mnjoo-real/sc4/out/fig1_modes.png

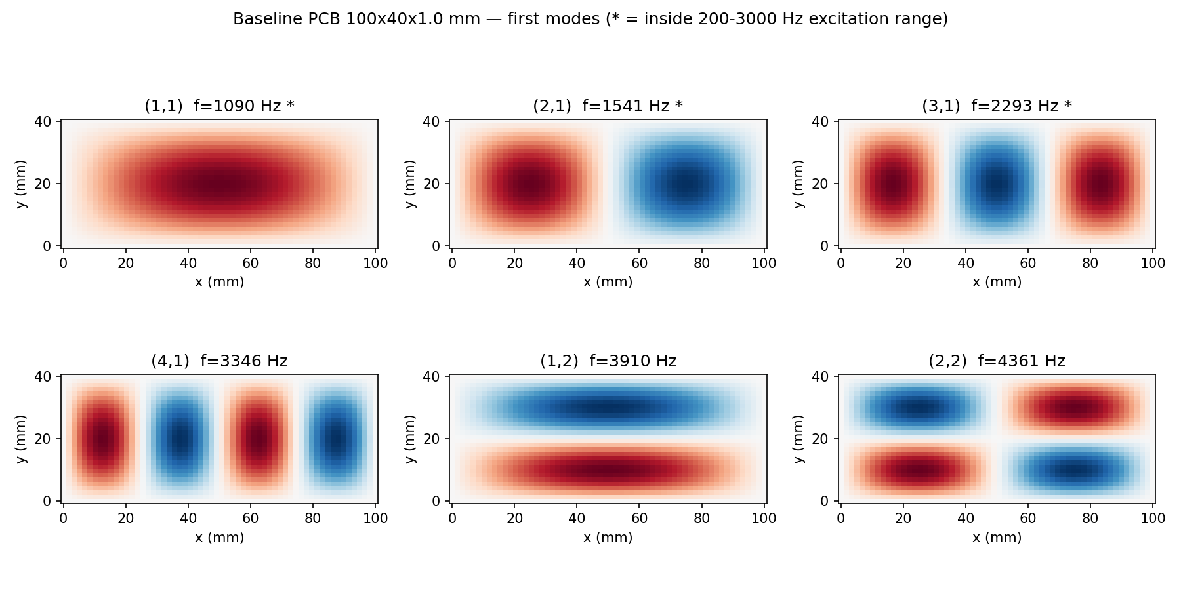
out/fig1_modes.png
