mnjoo-real/sc4/out/fig2_geometry_sweep.png

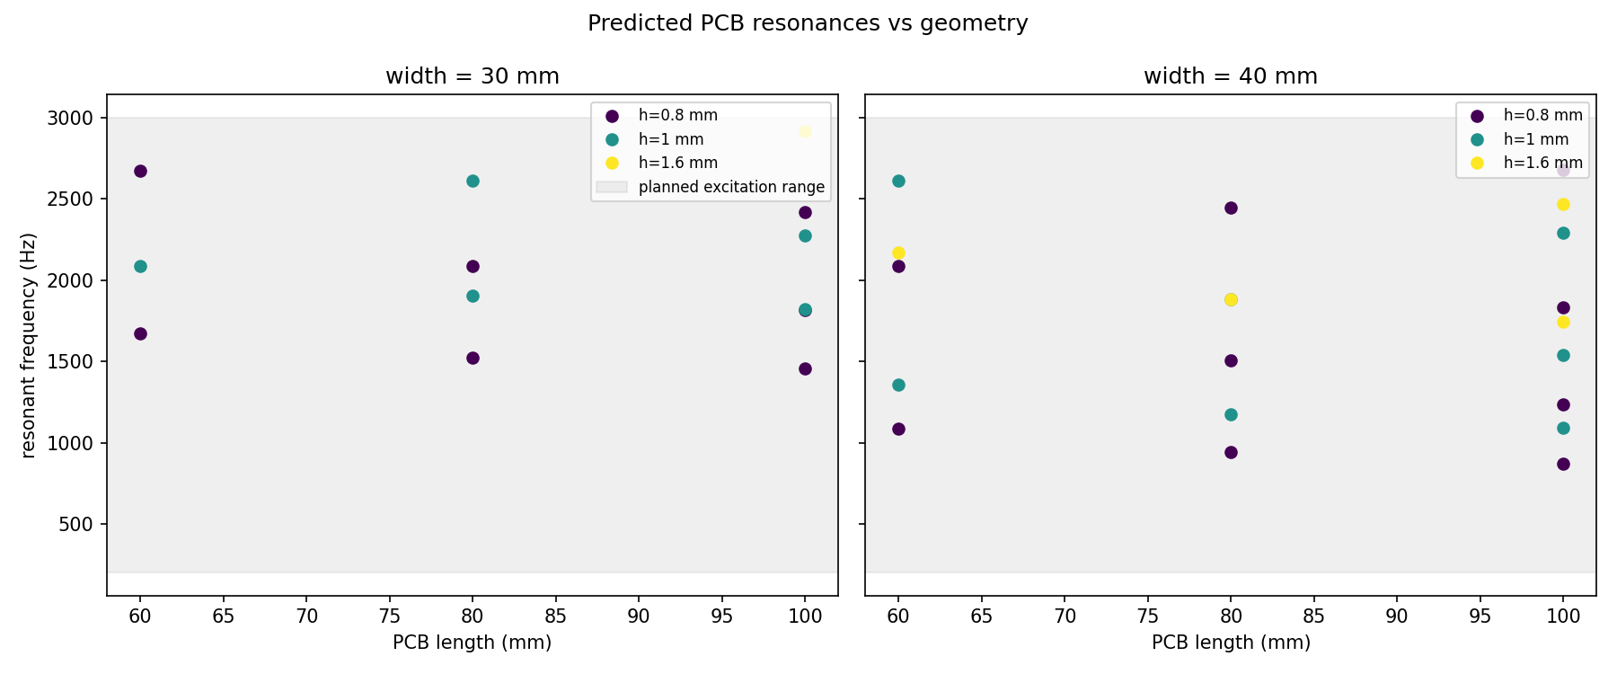
out/fig2_geometry_sweep.png
