mnjoo-real/sc4/out/fig3_frequency_response.png

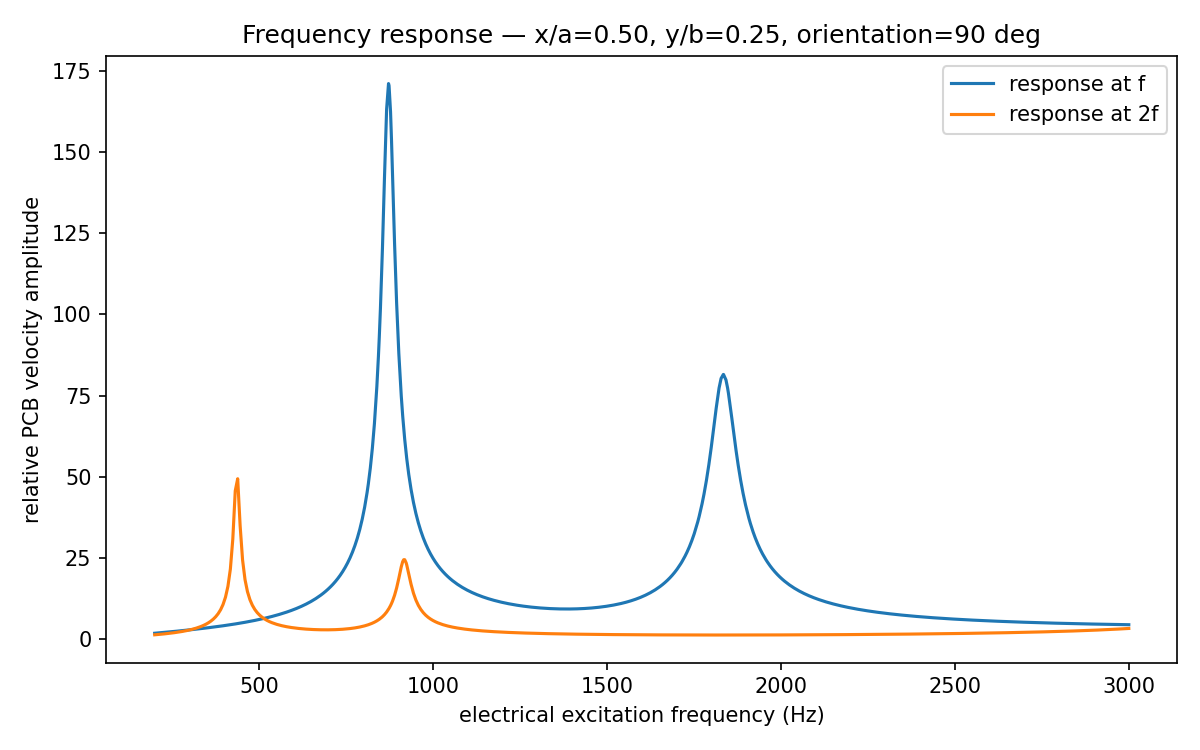
out/fig3_frequency_response.png
