mnjoo-real/sc4/out/fig4_position_map.png

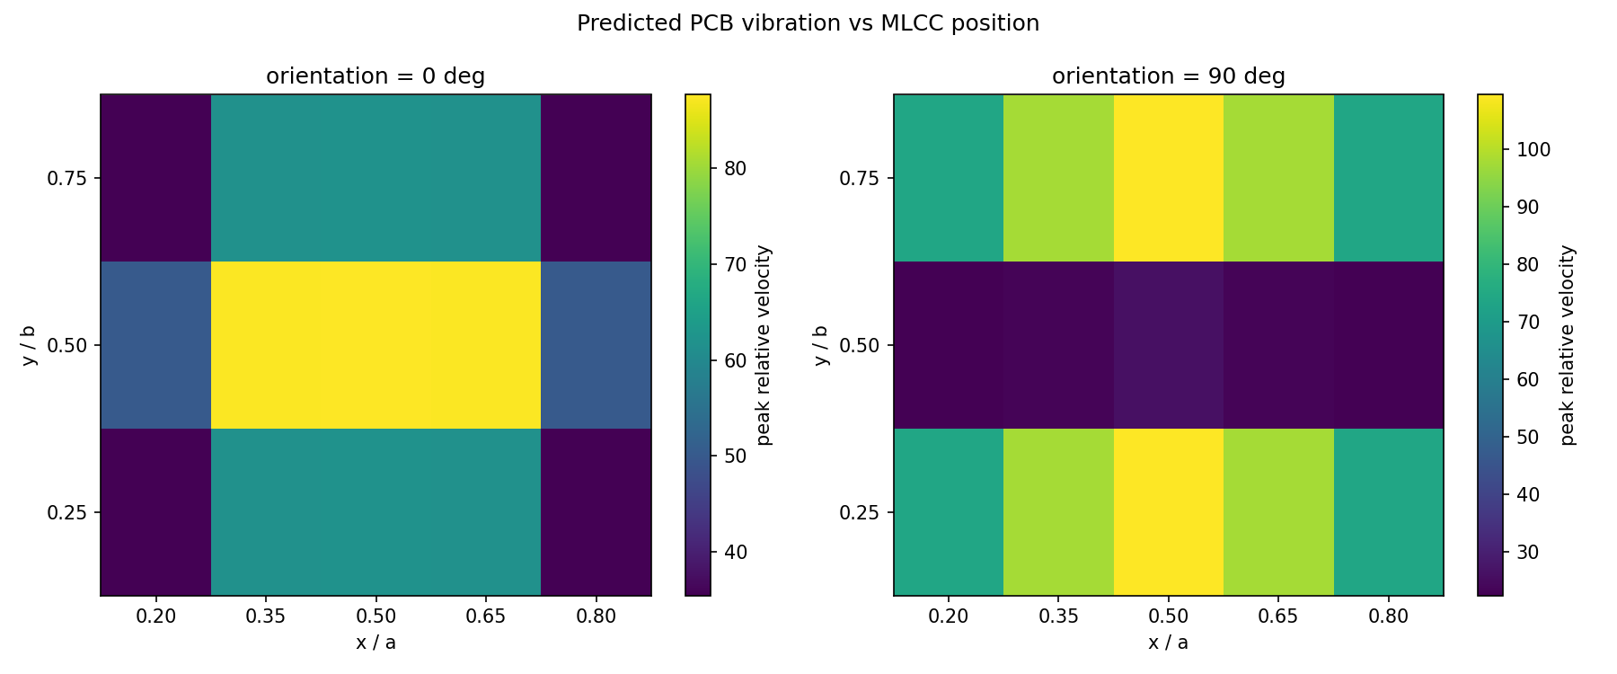
out/fig4_position_map.png
