mnjoo-real/sc4/out/fig5_orientation.png

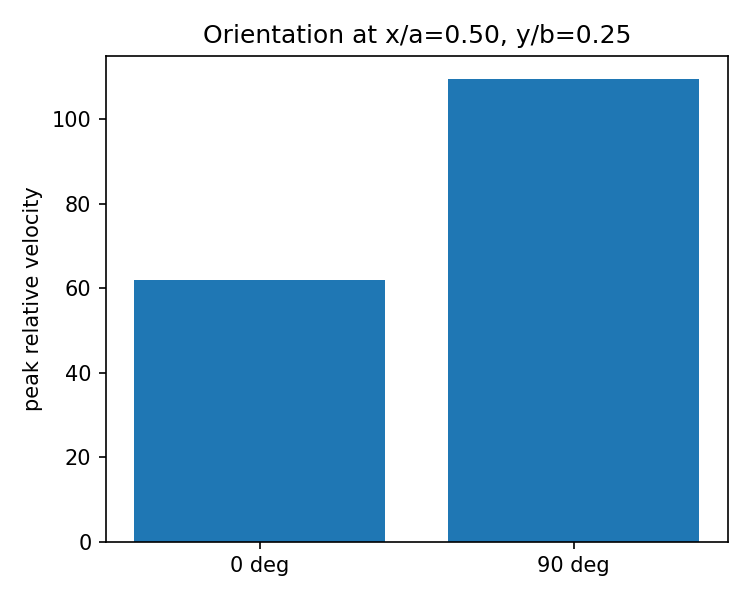
out/fig5_orientation.png
