mnjoo-real/sc4/out/fig6_pcb_robustness.png

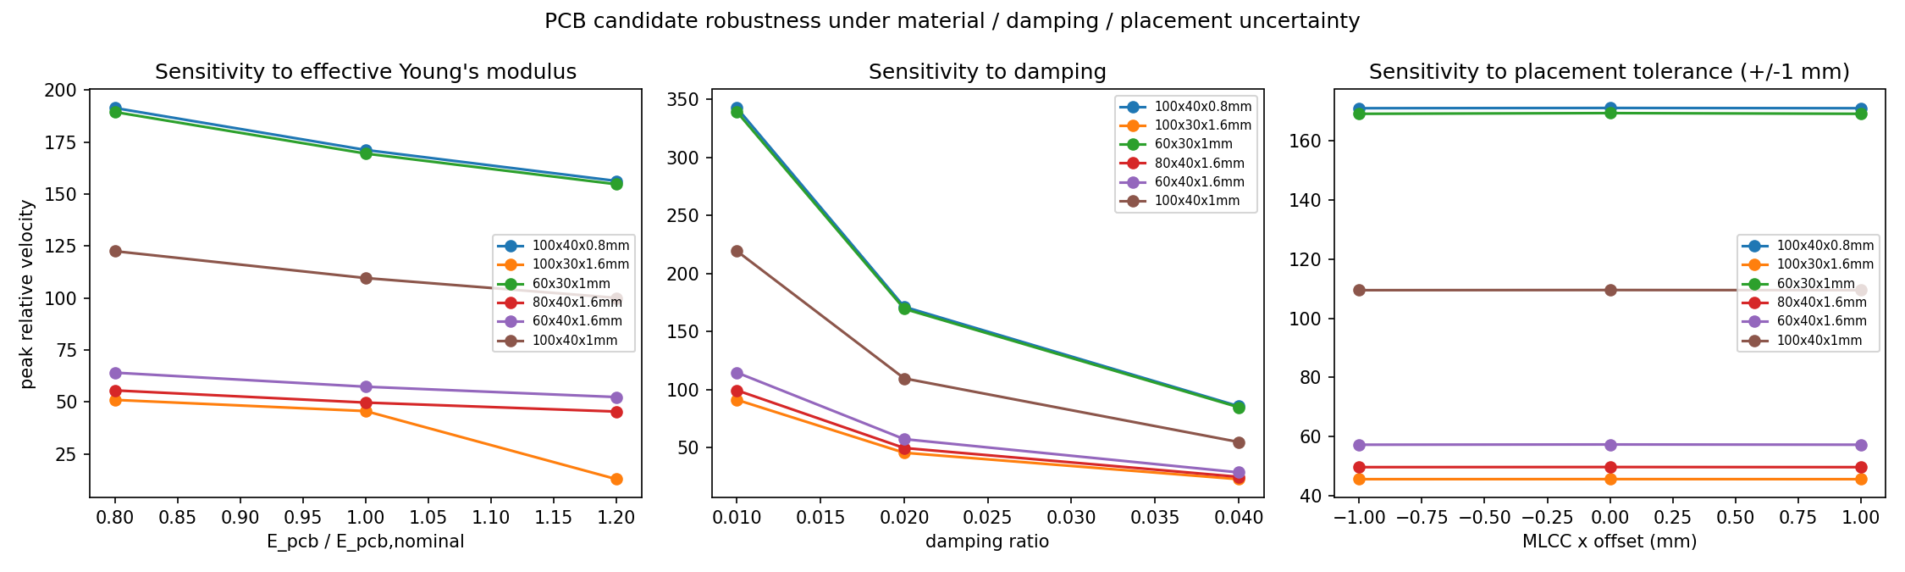
out/fig6_pcb_robustness.png
