mnjoo-real/sc4/pcb/PCB_5_VARIANT_COMPARISON.png

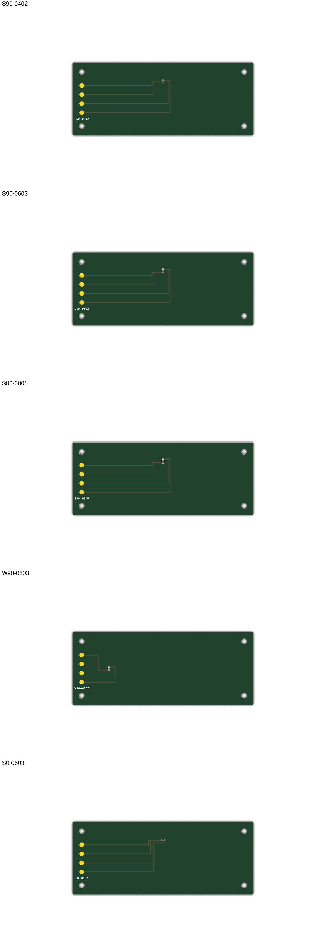
pcb/PCB_5_VARIANT_COMPARISON.png
