mnjoo-real/sc4/pcb/PCB_5_VARIANT_LAYOUT_SCHEMATIC_NOT_A_KICAD_RENDER.png

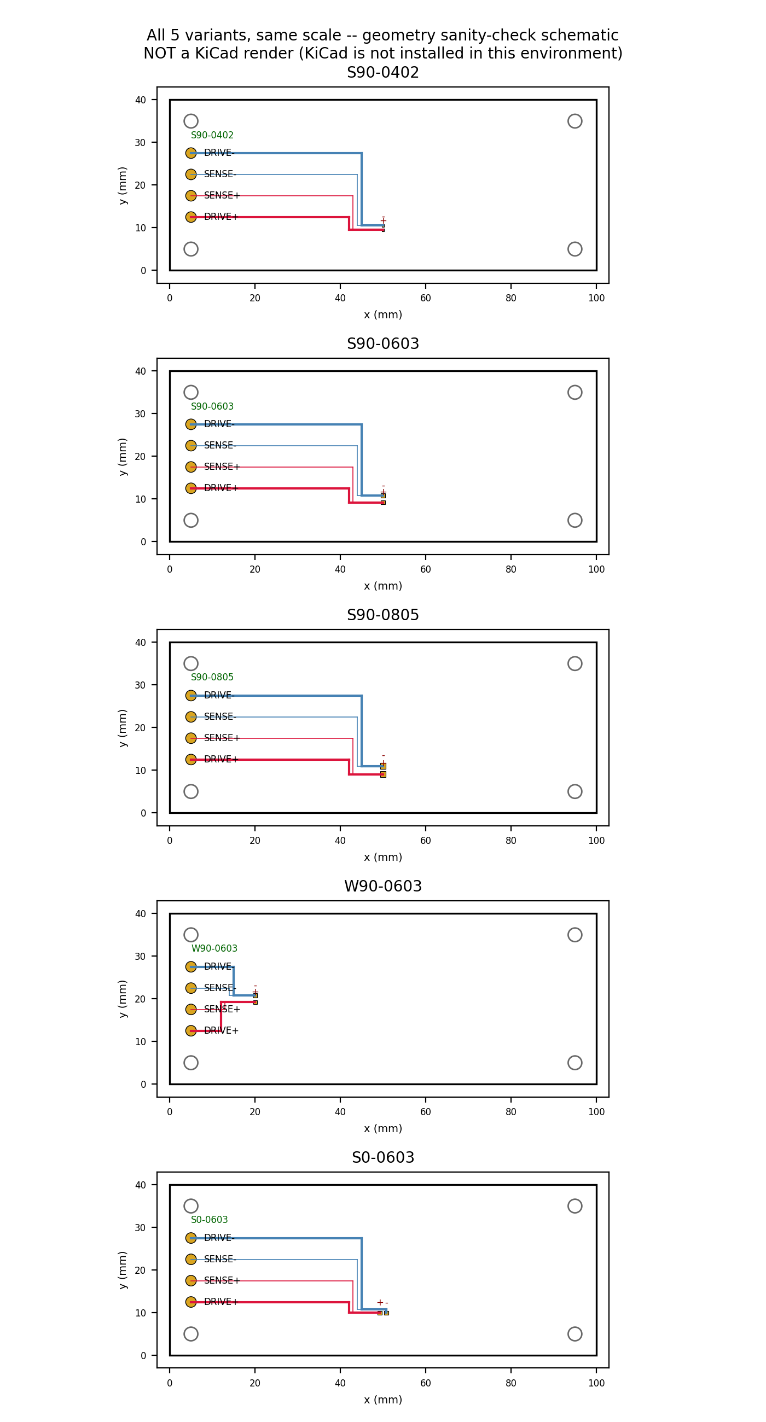
pcb/PCB_5_VARIANT_LAYOUT_SCHEMATIC_NOT_A_KICAD_RENDER.png
