mnjoo-real/sc4/pcb/S0-0603/renders/S0-0603_bottom.png

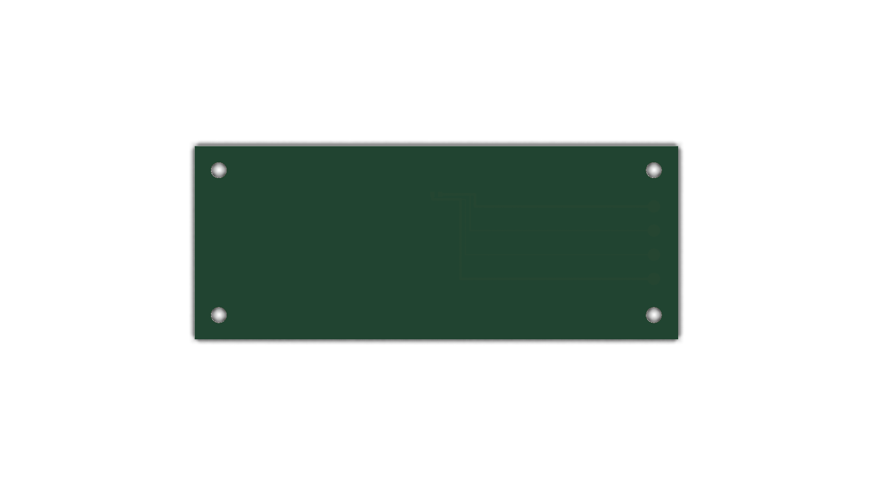
pcb/S0-0603/renders/S0-0603_bottom.png
