mnjoo-real/sc4/pcb/S0-0603/renders/S0-0603_layout_schematic_NOT_A_KICAD_RENDER.png

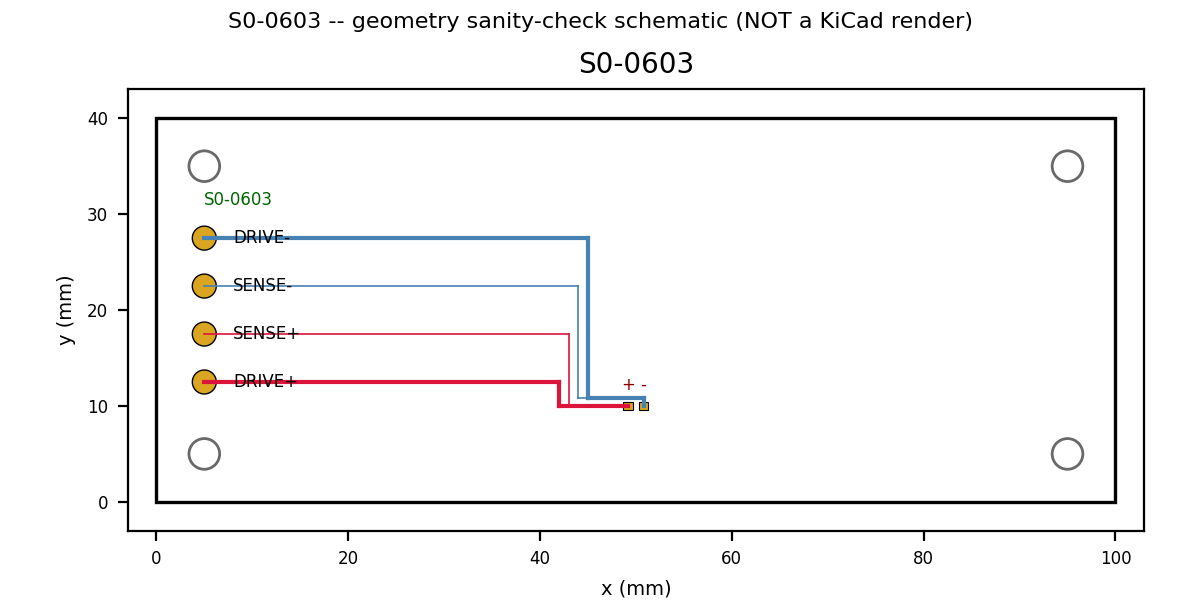
pcb/S0-0603/renders/S0-0603_layout_schematic_NOT_A_KICAD_RENDER.png
