mnjoo-real/sc4/pcb/S0-0603/manufacturing/gerber_verification/S0-0603_solder_mask.png

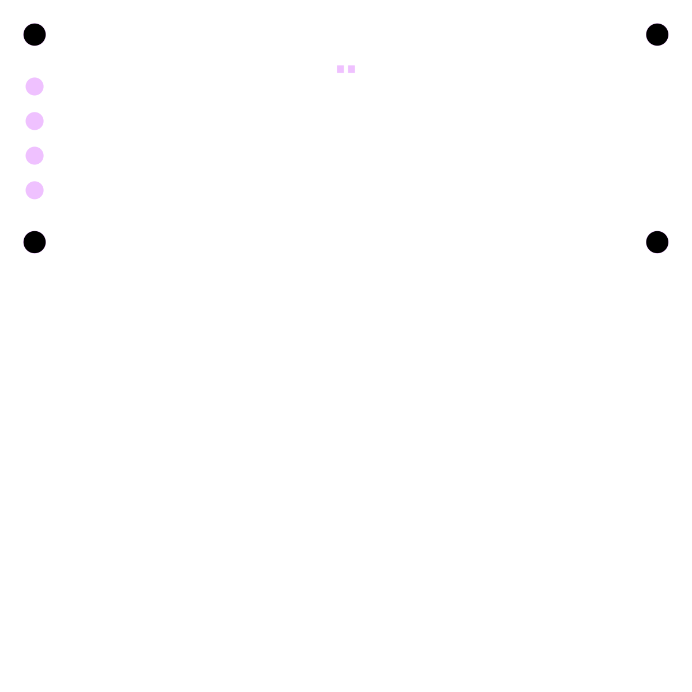
pcb/S0-0603/manufacturing/gerber_verification/S0-0603_solder_mask.png
