mnjoo-real/sc4/design/measurement_geometry.csv

element | x_mm | y_mm | z_mm | reference_frame | pointing | fixture | notes
PCB center | 50 | 20 | 0 | board coordinate frame: x=0-100mm (length), y=0-40mm (width), z=0 at PCB top surface | n/a - reference point | n/a | fixed reference point, identical for all 5 variants; independent of MLCC position, which differs by variant (see pcb_coordinates.csv)
microphone | 50 | 20 | 100 | same as PCB center | toward PCB, i.e. -z direction (straight down at the board) | required - fixed mic stand/boom | primary acoustic measurement; same position and fixture for every run and every board variant, deliberately independent of MLCC position so board-to-board comparisons are not confounded by a moving microphone
LDV target spot (optional) | variant-dependent (typically MLCC center) | variant-dependent | per-instrument standoff (TBD, per manufacturer spec) | same as PCB center | perpendicular to PCB top surface, small angle tolerance per instrument | optional - only when an LDV validation session is run | not required for baseline; target spot recorded per session in the run log, typically the MLCC location or board center for mode-shape spot checks
