mnjoo-real/sc4/pcb/S0-0603/manufacturing/gerber_verification/S0-0603_composite_top.png

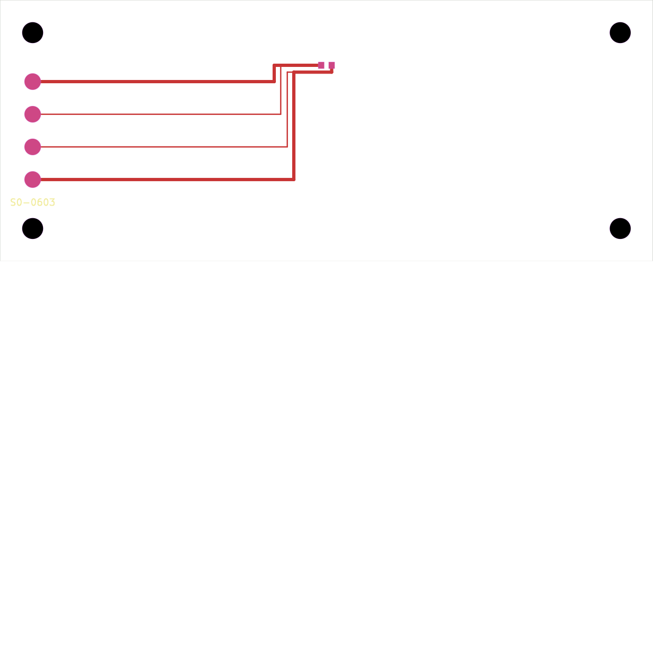
pcb/S0-0603/manufacturing/gerber_verification/S0-0603_composite_top.png
